intervigilium/bmw_m3_dct_shift_lights/m3_dct_shift_lights/m3_dct_shift_lights.sch

## EAGLE design m3_dct_shift_lights/m3_dct_shift_lights.sch (2021-04-12)

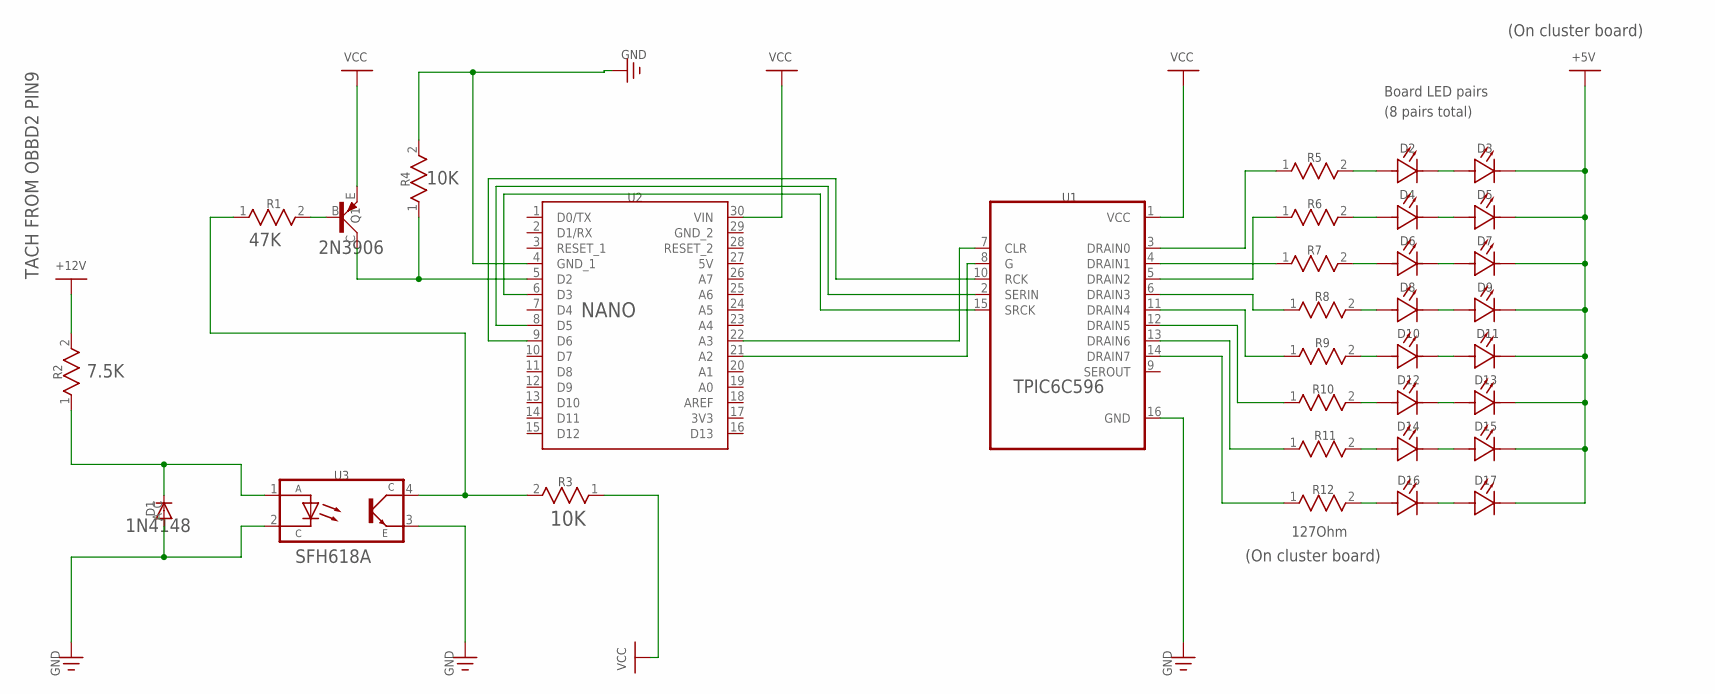
[picture p2: schematic m3_dct_shift_lights.sch]

Parts:
D1: 1N4148; DO35-10
Q1: 2N3906; TO92D
R1, R2, R3, R4: CFR1WSJT-52-10K; RESAD1490W55L950D360_AD1
R5, R6, R7, R8, R9, R10, R11, R12: ALSR0110R00JE12; RESAD1640W50L1112D360
U1: TPIC6C596N; DIP794W45P254L1969H508Q16
U2: A000005; MODULE_A000005
U3: SFH618A-2; DIP762W50P254L458H480Q4

Connections:
Net_0: U1.15 (SRCK), U2.6 (D3)
Net_1: U1.2 (SERIN), U2.8 (D5)
Net_2: U1.10 (RCK), U2.9 (D6)
Net_3: U1.7 (CLR), U2.22 (A3)
Net_4: U1.8 (G), U2.21 (A2)
Net_5: Q1.C, R4.1, U2.5 (D2)
Net_6: D1.C, R2.1, U3.1 (A)
Net_7: D1.A, R4.2, U1.16 (GND), U2.4 (GND_1), U3.2 (C), U3.3 (E)
Net_8: Q1.B, R1.2
Net_9: R1.1, R3.2, U3.4 (CO)
Net_10: Q1.E, R3.1, U1.1 (VCC), U2.30 (VIN)
Net_11: R2.2
Net_12: R5.2
Net_13: R6.2
Net_14: R7.2
Net_15: R8.2
Net_16: R9.2
Net_17: R10.2
Net_18: R11.2
Net_19: R12.2
Net_20: R12.1, U1.14 (DRAIN7)
Net_21: R11.1, U1.13 (DRAIN6)
Net_22: R10.1, U1.12 (DRAIN5)
Net_23: R9.1, U1.11 (DRAIN4)
Net_24: R8.1, U1.6 (DRAIN3)
Net_25: R7.1, U1.5 (DRAIN2)
Net_26: R6.1, U1.4 (DRAIN1)
Net_27: R5.1, U1.3 (DRAIN0)

Notes on the sheet:
7.5K
47K
1N4148
2N3906
10K
SFH618A
NANO
TPIC6C596
TACH FROM OBBD2 PIN9
127Ohm
(On cluster board)
Board LED pairs (8 pairs total)
VCC
GND
+12V
R10
R11
R12
D10
D11
D12
D13
D14
D15
D16
D17
+5V
